aditi-23-singh/STM32_Projects/Project/Core/Inc/Motor_Controller.h

#ifndef INC_MOTOR_CONTROLLER_H_
#define INC_MOTOR_CONTROLLER_H_

#include "stm32f0xx_hal.h"
#include "stm32f0xx.h"

typedef struct{
	volatile uint8_t running;
	uint32_t steps_remaining;
	uint32_t period_us;
	uint8_t direction;
	uint32_t accumulator_us;
} MotorController_t;

#define STEP_PULSE_WIDTH_US 40
extern MotorController_t MotorControl;

void Motor_Init(void);

void Delay_us(uint32_t us);

void Motor_Update(void);

#endif
