aditi-23-singh/STM32_Projects/Project/Core/Inc/KeypadHandler.h

#ifndef KEYPADHANDLER_H
#define KEYPADHANDLER_H

#include "Keypad.h"
#include "Common.h"

typedef struct {
    EVENT_CODES_ENUM CurrentEvent;
    EVENT_CODES_ENUM PreviousEvent;
    bool NewEventReceived;
    KeypadKey_t CurrentKey;
    char CurrentChar;
} KeyPadHandlerTypedefStruct;

void KeypadHandler_Init(void);
void UpdateKeypad(void);

#endif
