aditi-23-singh/STM32_Projects/Project/Core/Inc/LCDApplication.h

#ifndef INC_LCDAPPLICATION_H_
#define INC_LCDAPPLICATION_H_

#include "main.h"
typedef enum {
    DISPLAY_MODE_IDLE = 0,
    DISPLAY_MODE_SINGLE = 1,
    DISPLAY_MODE_DOUBLE = 2,
    DISPLAY_MODE_HOLD = 3
} DisplayMode_t;

typedef enum {
    LED_STATUS_OFF = 0,
    LED_STATUS_FAST_BLINK = 1,
    LED_STATUS_SLOW_BLINK = 2,
    LED_STATUS_HOLD = 3
} LEDStatus_t;


void LCDApplication_Init(void);
void LCDApplication_Process();
void LCDApplication_UpdateLocalLED(LEDStatus_t status);
void LCD_UpdateLocalMode(DisplayMode_t mode);
void LCD_UpdateLocalLED(LEDStatus_t status);
void LCDApplication_UpdateRemoteMode(DisplayMode_t mode);
void LCDApplication_UpdateRemoteLED(LEDStatus_t status);
void LCD_UpdateRemoteMode(DisplayMode_t mode);
void LCD_SyncRemoteEvent(uint8_t event);
void LCD_SyncLocalEvent(uint8_t event);
void LCD_UpdateRemoteLED(LEDStatus_t status);
void LCD_UpdateLocalStatus(uint8_t status);
void LCD_UpdateRemoteStatus(uint8_t status);
void LCD_UpdateStatusDisplay(void);


#endif
